jsteele22/telescopes/src/media/incoming/PXL_20240909_195538547.jpg

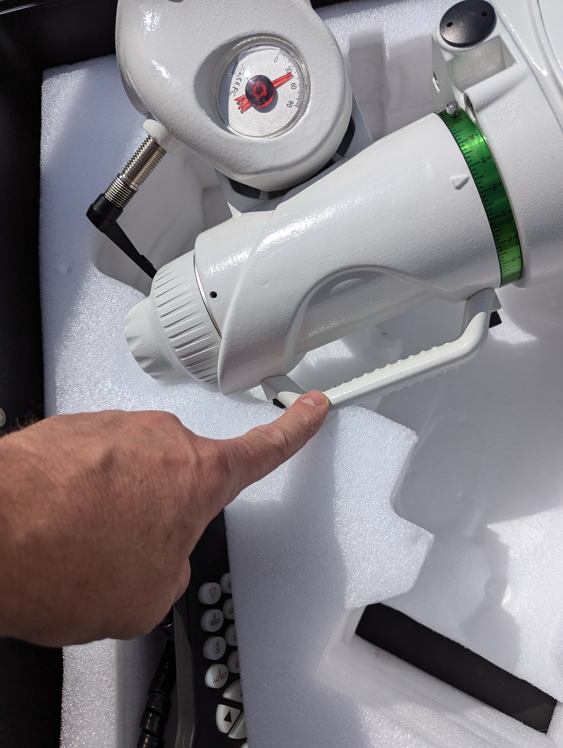
src/media/incoming/PXL_20240909_195538547.jpg
