jsteele22/telescopes/src/media/incoming/PXL_20240909_195637339.jpg

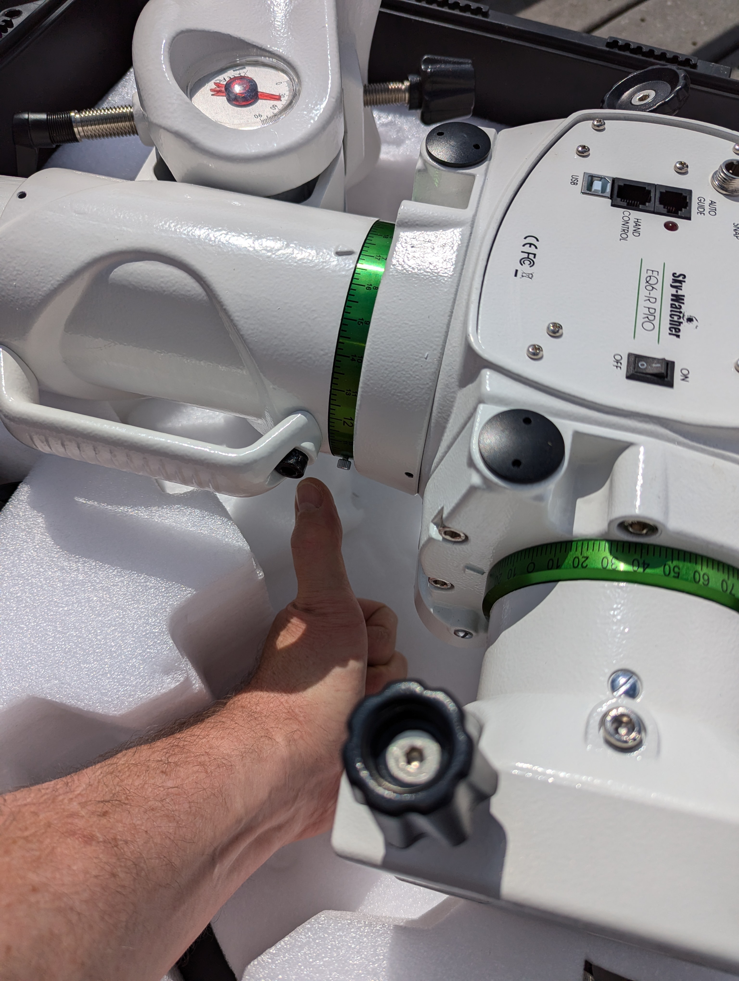
src/media/incoming/PXL_20240909_195637339.jpg
