jsteele22/telescopes/src/media/incoming/PXL_20240909_200801944.jpg

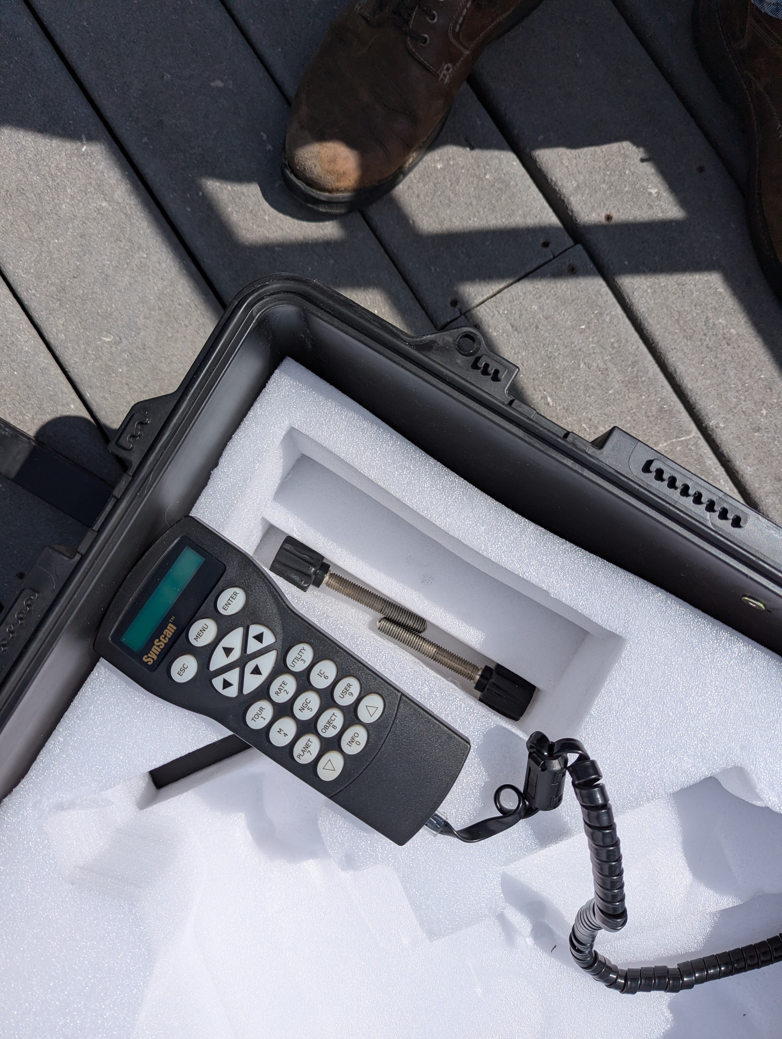
src/media/incoming/PXL_20240909_200801944.jpg
