jsteele22/telescopes/src/media/incoming/PXL_20240909_200844961.jpg

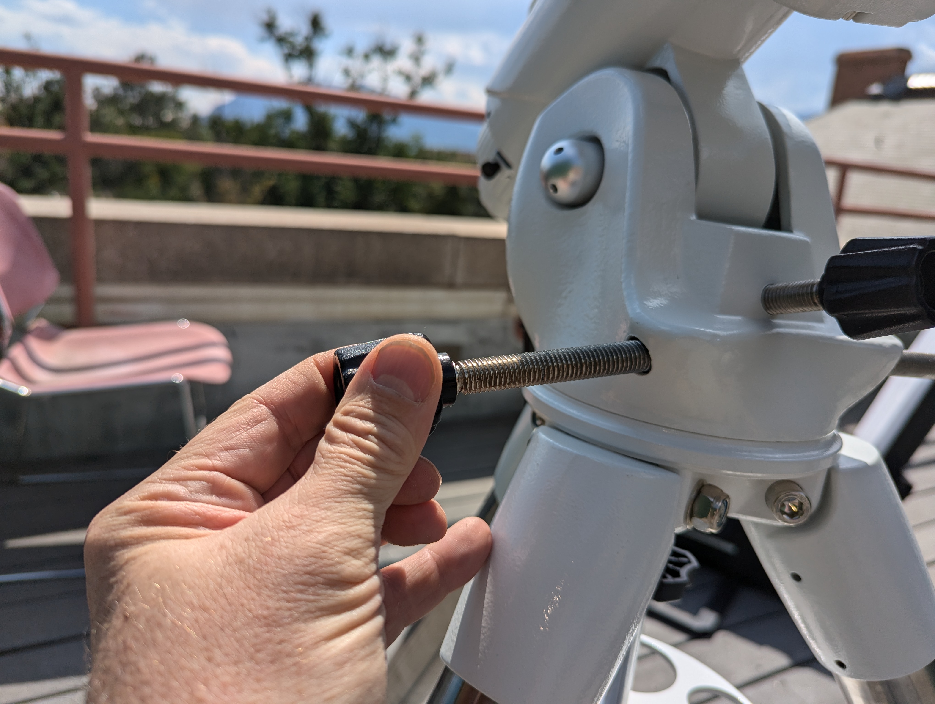
src/media/incoming/PXL_20240909_200844961.jpg
