jsteele22/telescopes/src/media/incoming/PXL_20240909_201119024.PANO.jpg

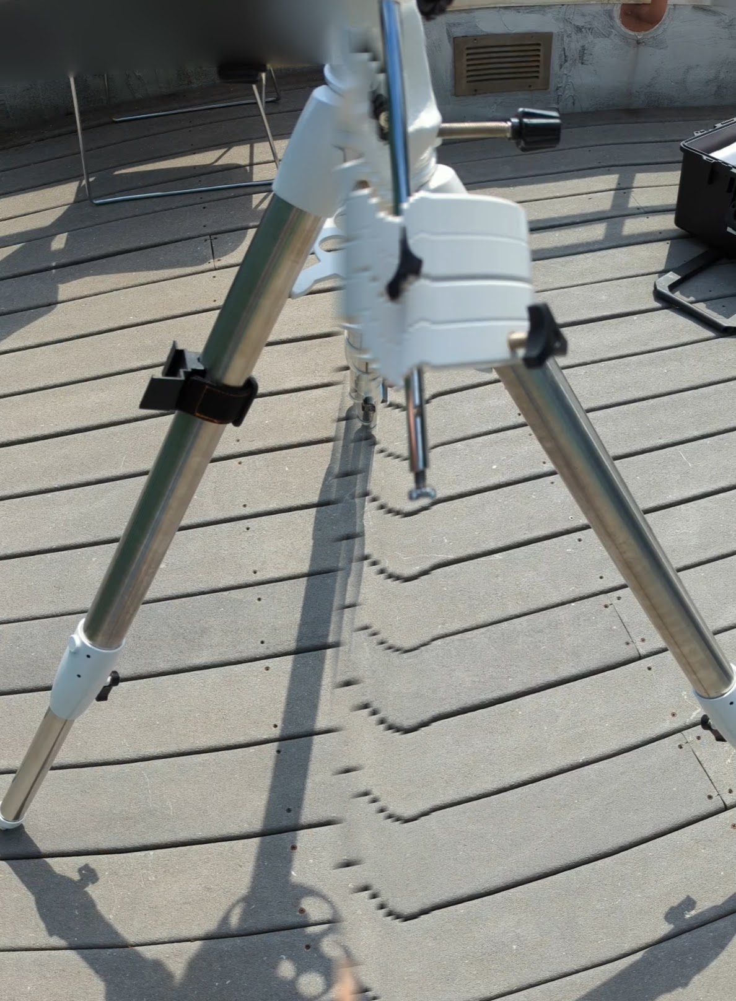
src/media/incoming/PXL_20240909_201119024.PANO.jpg
