jsteele22/telescopes/src/media/incoming/PXL_20240909_201218590.jpg

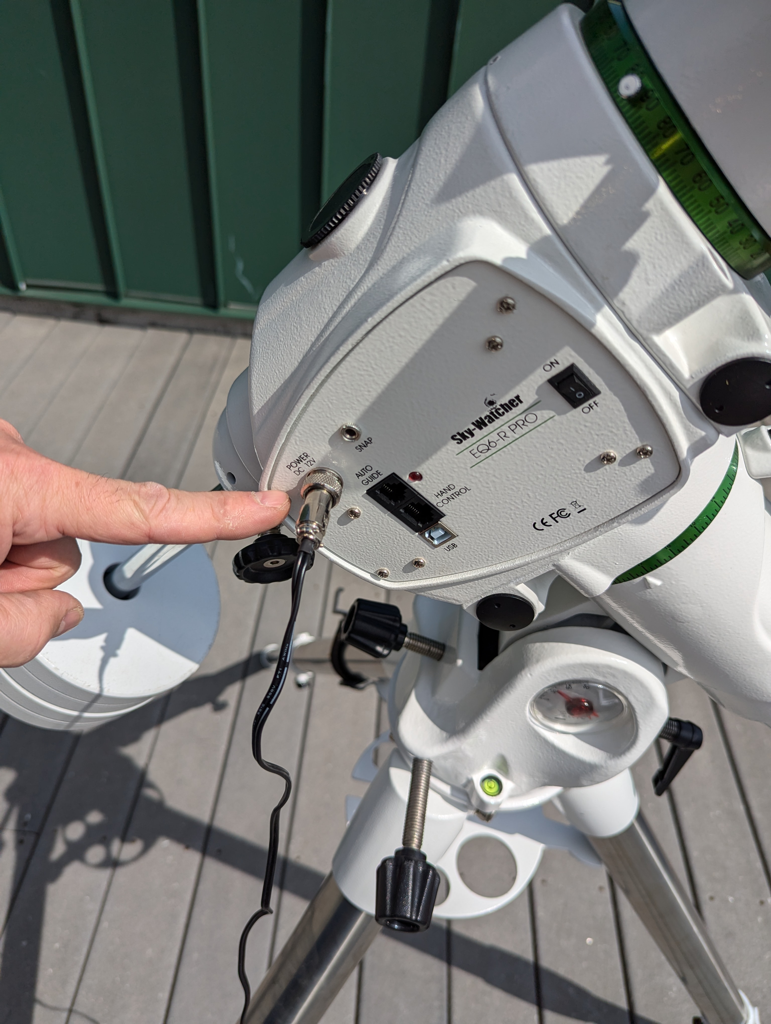
src/media/incoming/PXL_20240909_201218590.jpg
