jsteele22/telescopes/src/media/incoming/PXL_20240910_205359571.jpg

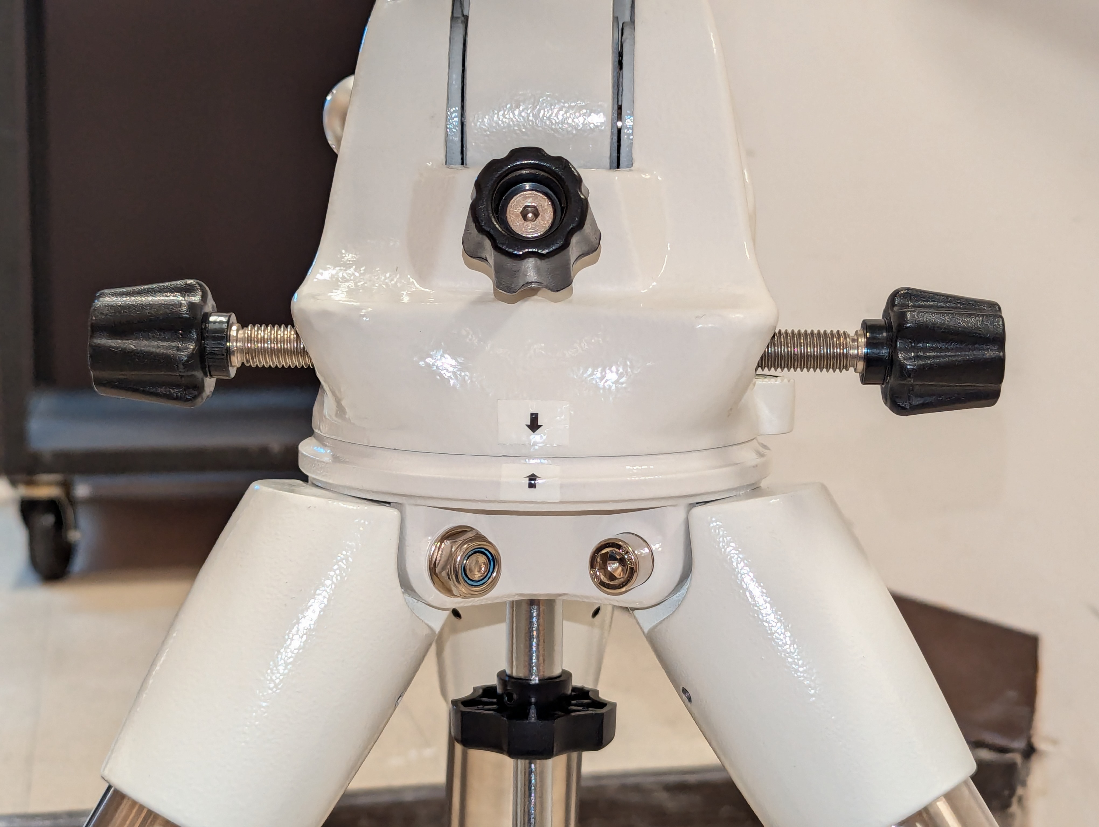
src/media/incoming/PXL_20240910_205359571.jpg
