jsteele22/telescopes/src/media/incoming/PXL_20240910_215625529.jpg

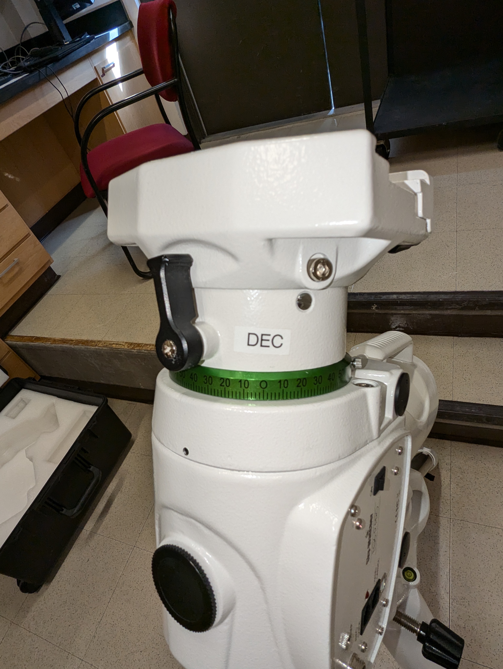
src/media/incoming/PXL_20240910_215625529.jpg
