jsteele22/telescopes/src/media/incoming/PXL_20240910_215647571.jpg

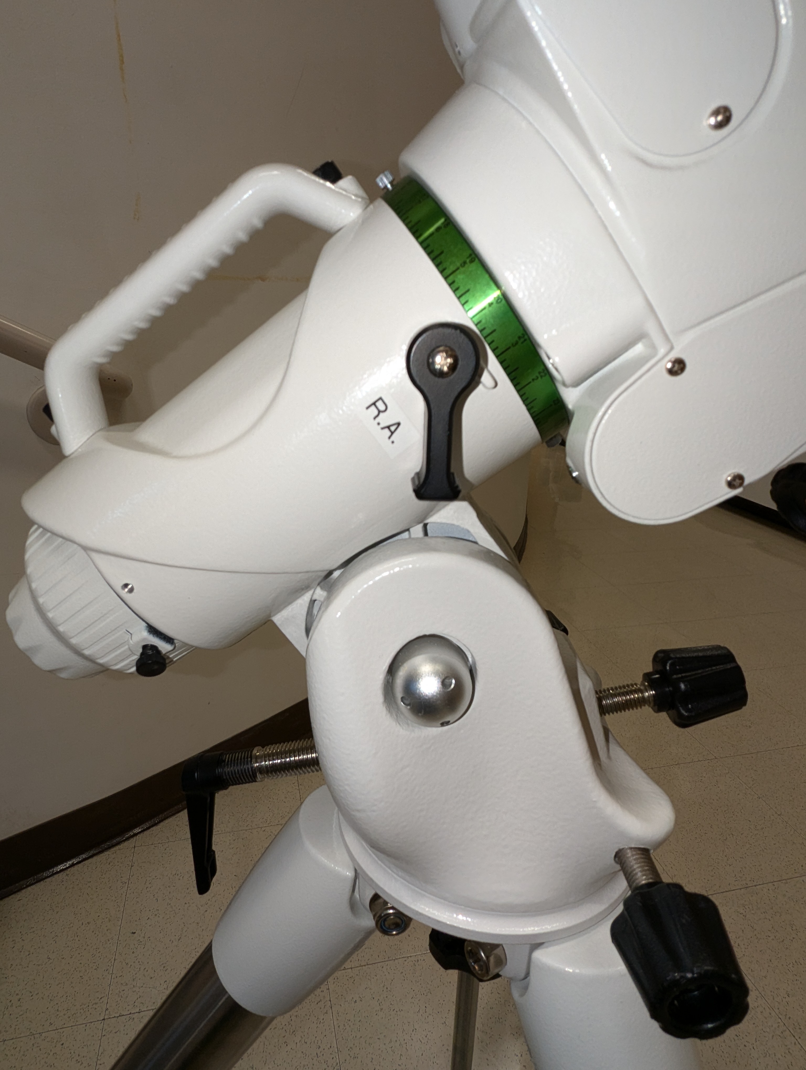
src/media/incoming/PXL_20240910_215647571.jpg
