jsteele22/telescopes/src/media/incoming/PXL_20240910_215757097.jpg

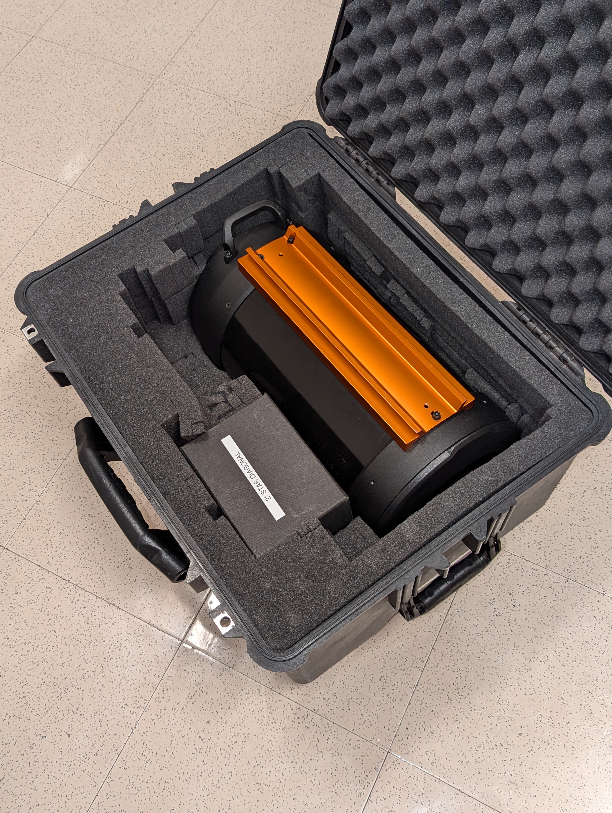
src/media/incoming/PXL_20240910_215757097.jpg
