jsteele22/telescopes/src/media/incoming/PXL_20240910_220001010.jpg

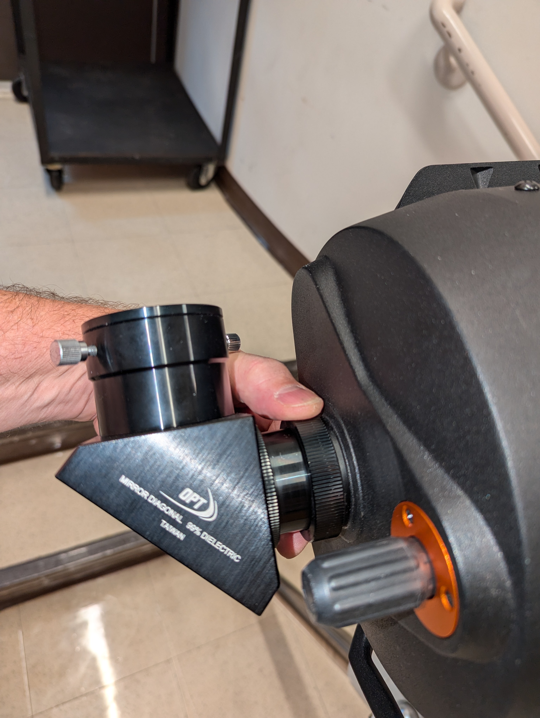
src/media/incoming/PXL_20240910_220001010.jpg
