jsteele22/telescopes/src/media/incoming/PXL_20240910_220033113.jpg

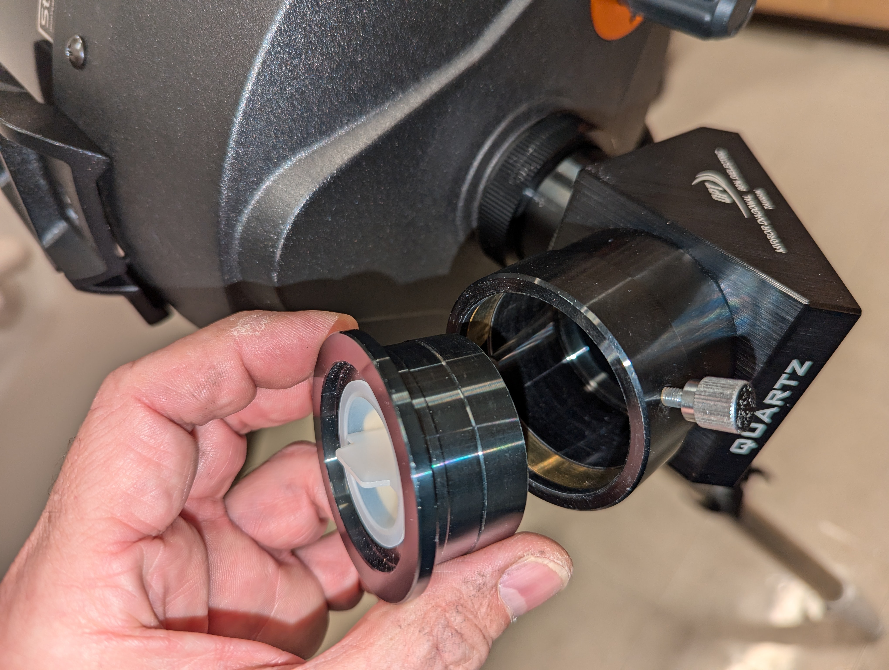
src/media/incoming/PXL_20240910_220033113.jpg
