jsteele22/telescopes/src/media/incoming/PXL_20240910_220900610.jpg

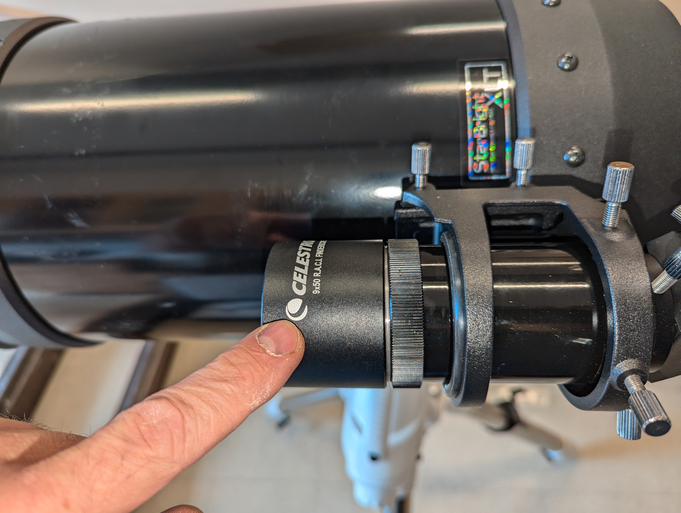
src/media/incoming/PXL_20240910_220900610.jpg
