jsteele22/telescopes/src/media/incoming/PXL_20240910_220907315.jpg

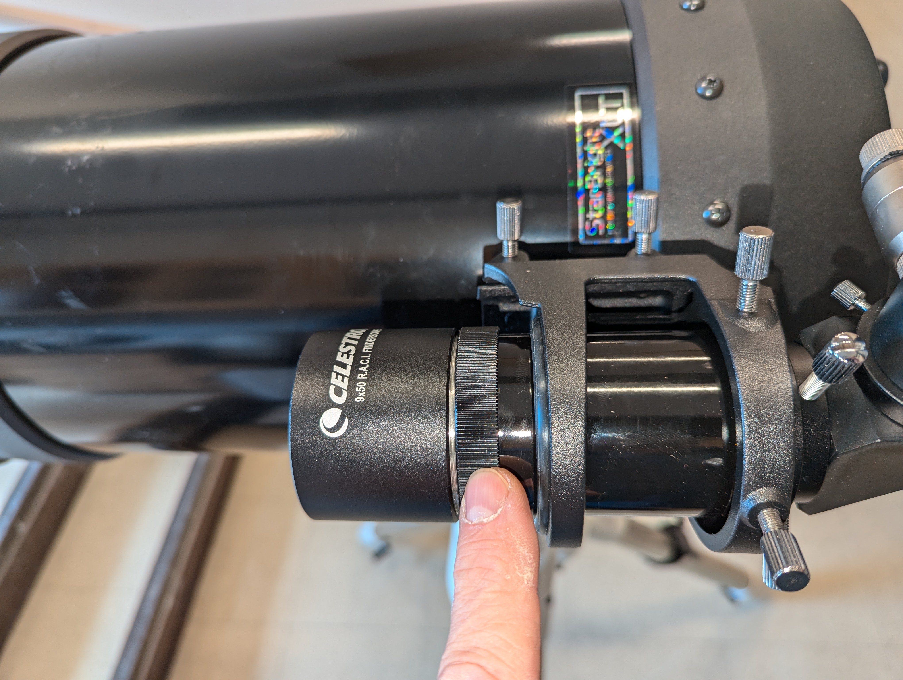
src/media/incoming/PXL_20240910_220907315.jpg
