jsteele22/telescopes/src/media/incoming/PXL_20240910_220939257.jpg

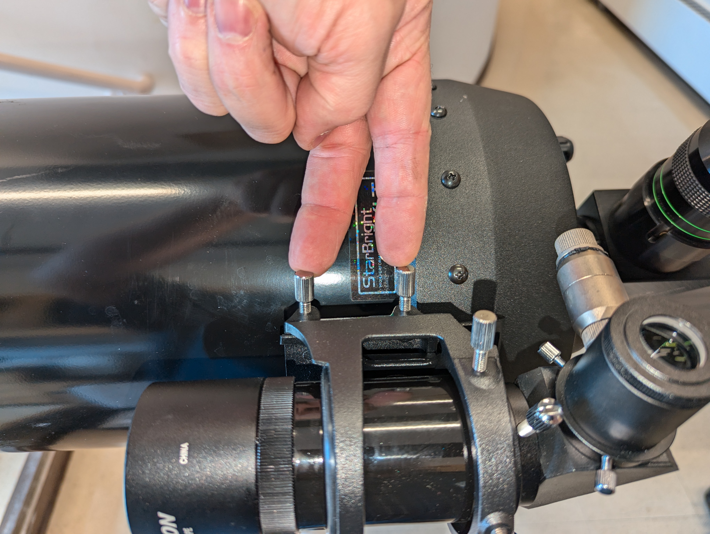
src/media/incoming/PXL_20240910_220939257.jpg
