jsteele22/telescopes/src/media/incoming/PXL_20240910_221006159.jpg

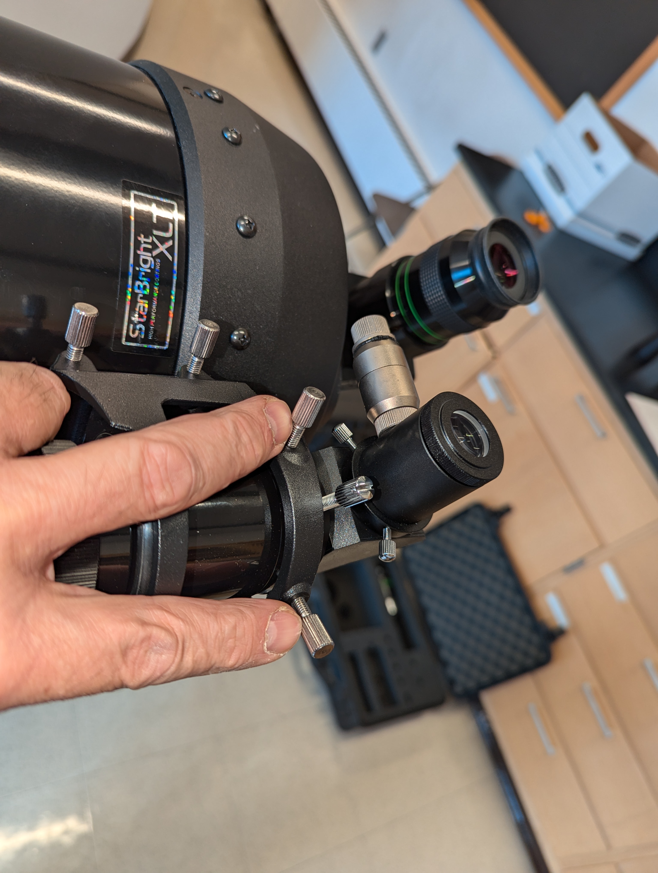
src/media/incoming/PXL_20240910_221006159.jpg
