jsteele22/telescopes/src/media/incoming/PXL_20240910_221018687.jpg

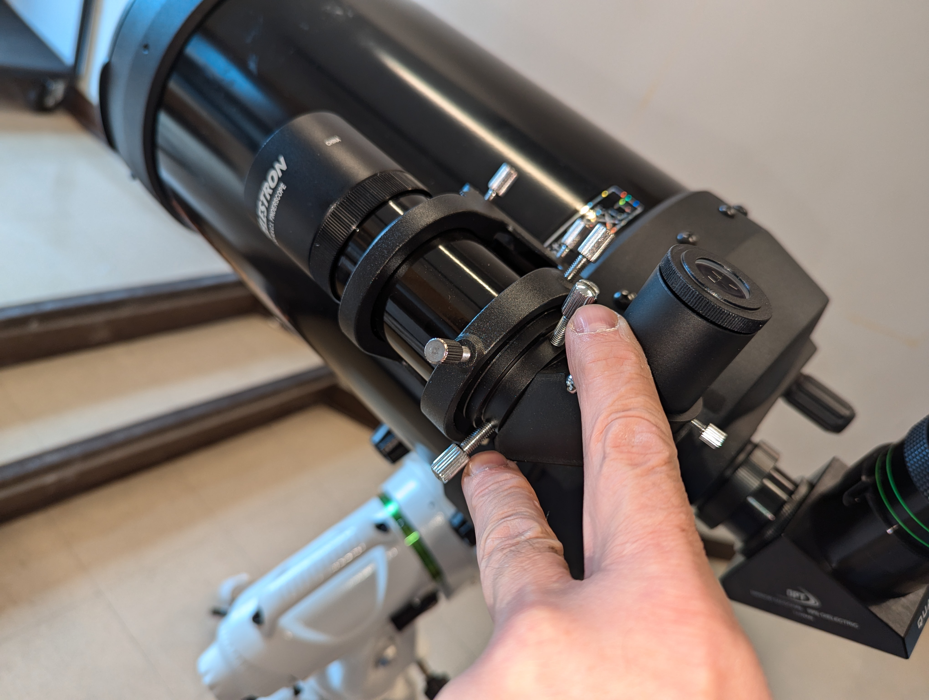
src/media/incoming/PXL_20240910_221018687.jpg
