jsteele22/telescopes/src/media/incoming/PXL_20240910_221028572.jpg

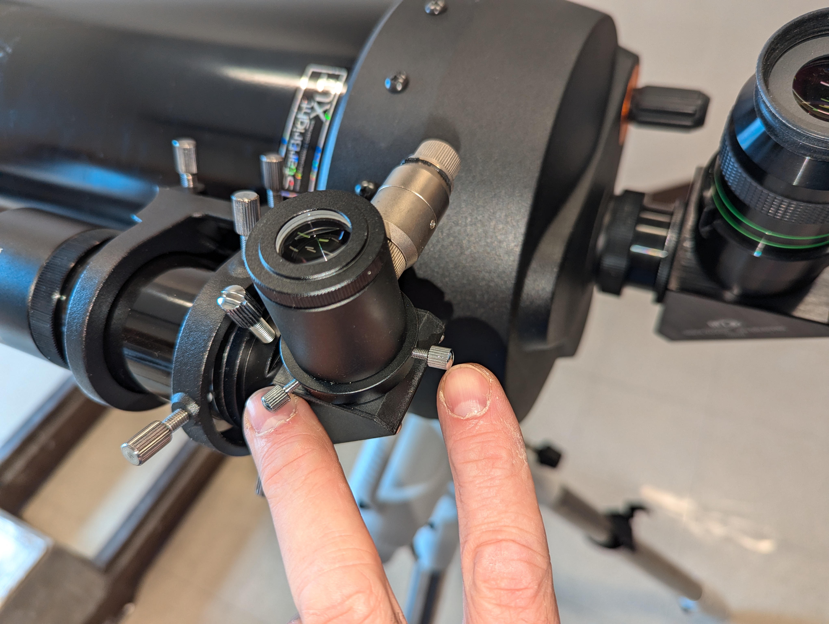
src/media/incoming/PXL_20240910_221028572.jpg
