jsteele22/telescopes/src/media/incoming/PXL_20240910_221039068.jpg

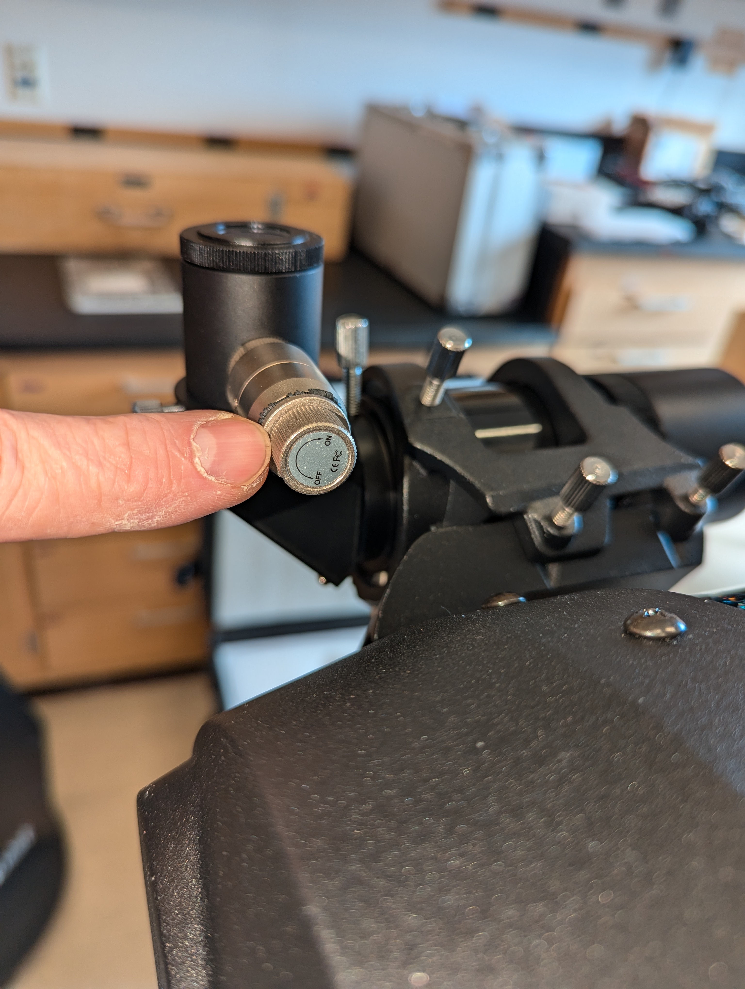
src/media/incoming/PXL_20240910_221039068.jpg
