jsteele22/telescopes/src/media/pub/eq6_DEC_clutch.jpg

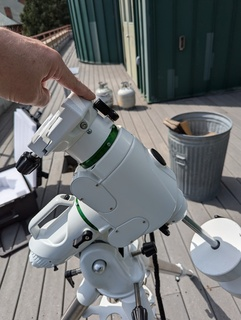
src/media/pub/eq6_DEC_clutch.jpg
