jsteele22/telescopes/src/media/raw/eq6_alignment_bolts.jpg

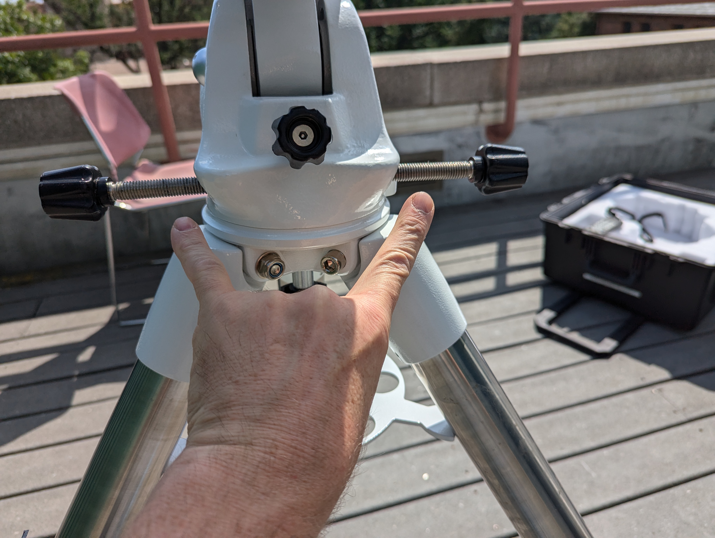
src/media/raw/eq6_alignment_bolts.jpg
