jsteele22/telescopes/src/media/raw/eq6_alignment_hole.jpg

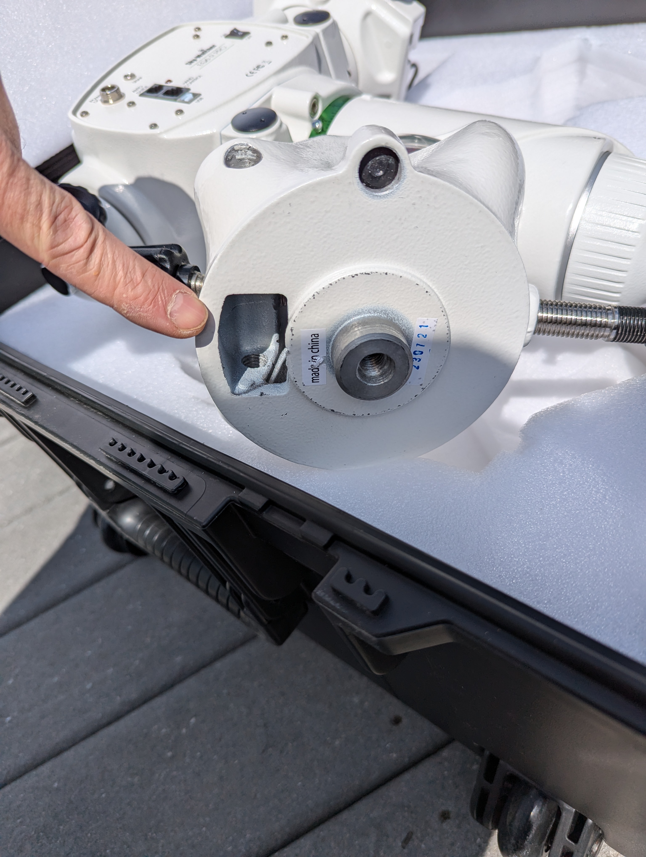
src/media/raw/eq6_alignment_hole.jpg
