jsteele22/telescopes/src/media/raw/eq6_cables.jpg

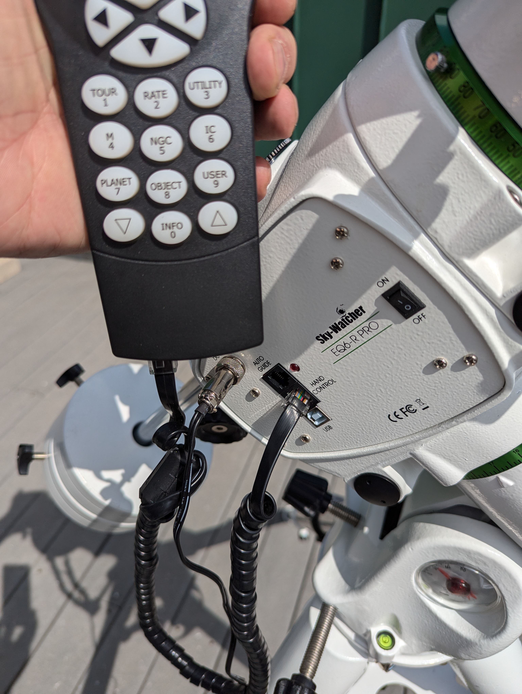
src/media/raw/eq6_cables.jpg
