jsteele22/telescopes/src/media/raw/eq6_OTA_prep.jpg

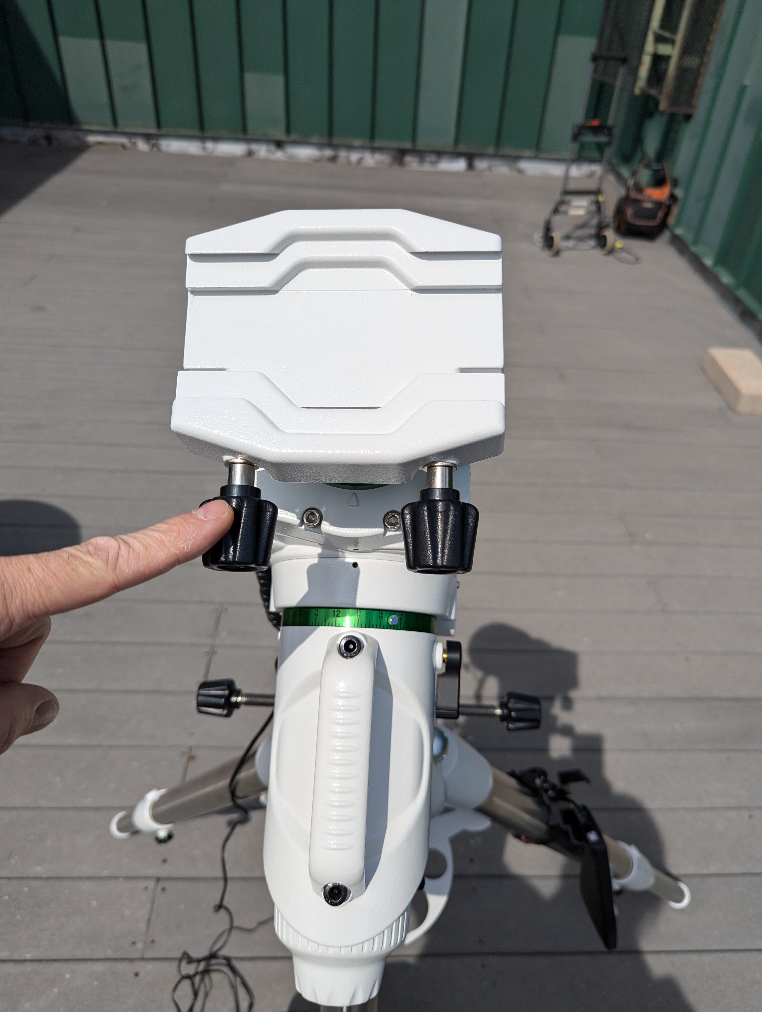
src/media/raw/eq6_OTA_prep.jpg
