jsteele22/telescopes/src/media/raw/eq6_pelican.jpg

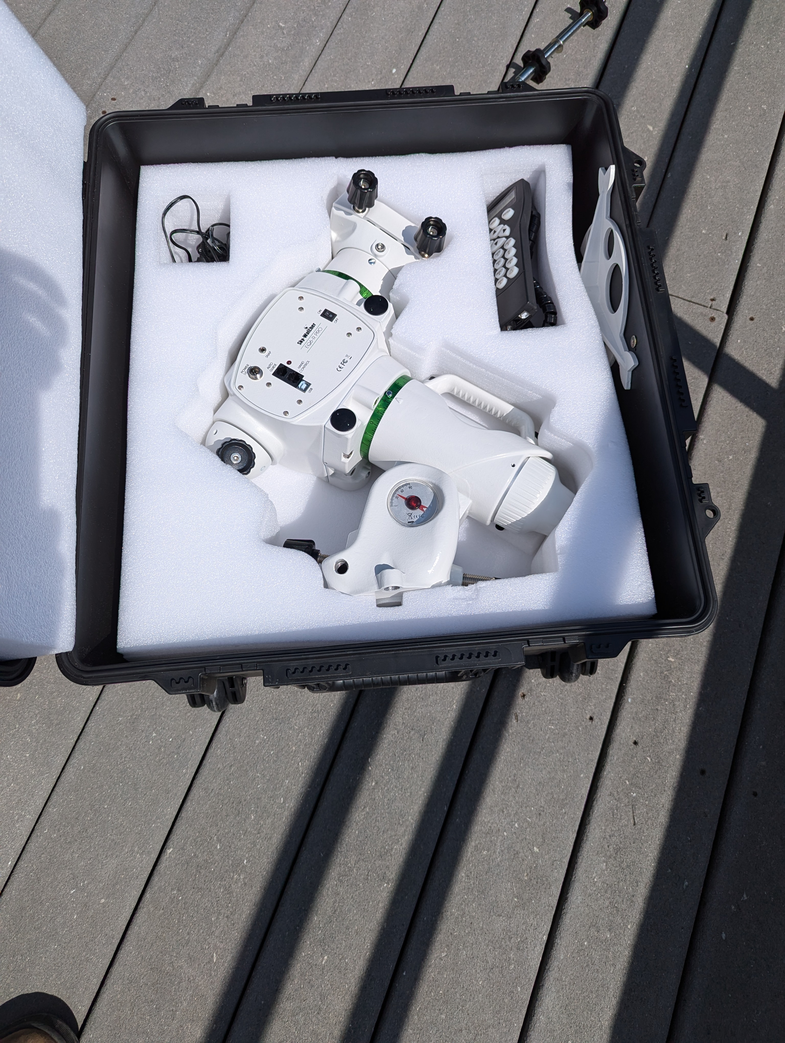
src/media/raw/eq6_pelican.jpg
