jsteele22/telescopes/src/media/raw/eq6_RA_clutch.jpg

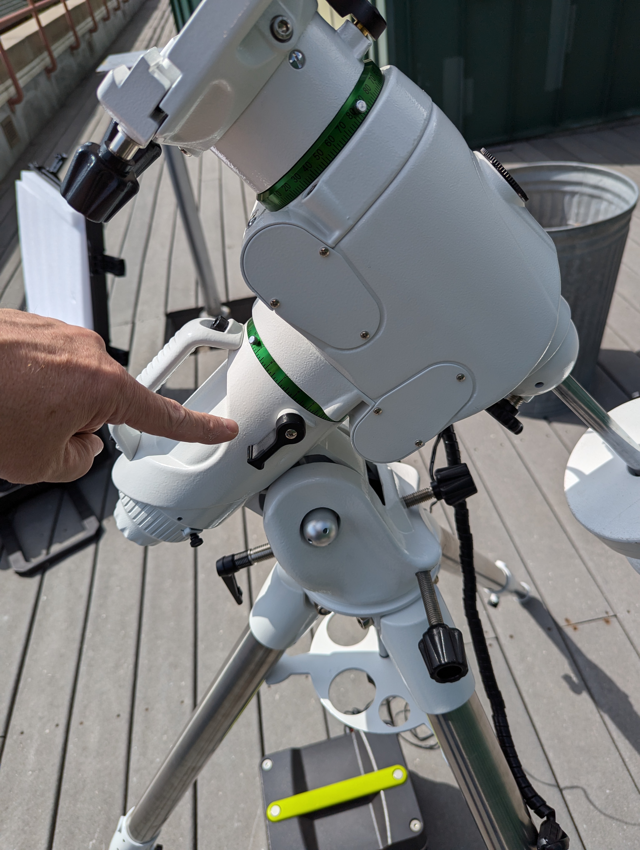
src/media/raw/eq6_RA_clutch.jpg
