jsteele22/telescopes/src/media/raw/eq6_toesaver.jpg

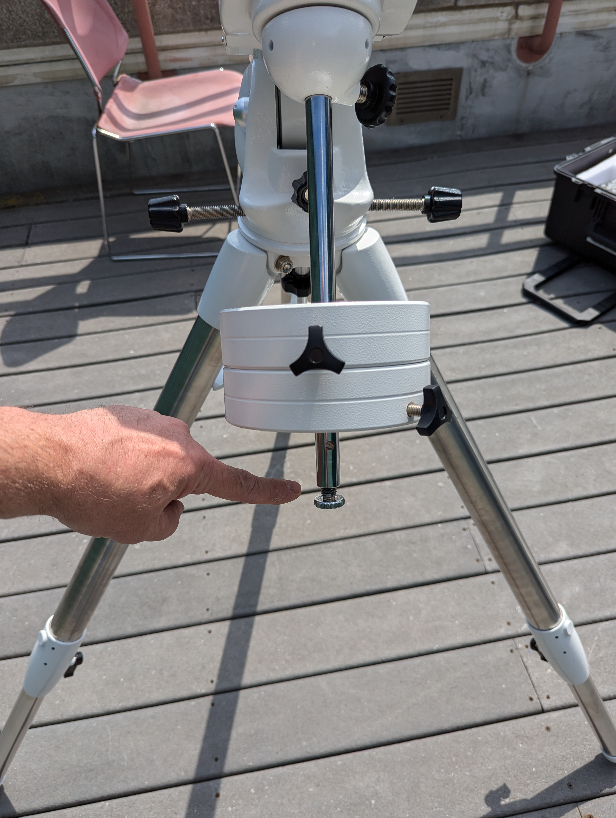
src/media/raw/eq6_toesaver.jpg
