jsteele22/telescopes/src/media/raw/eq6_tripod_top.jpg

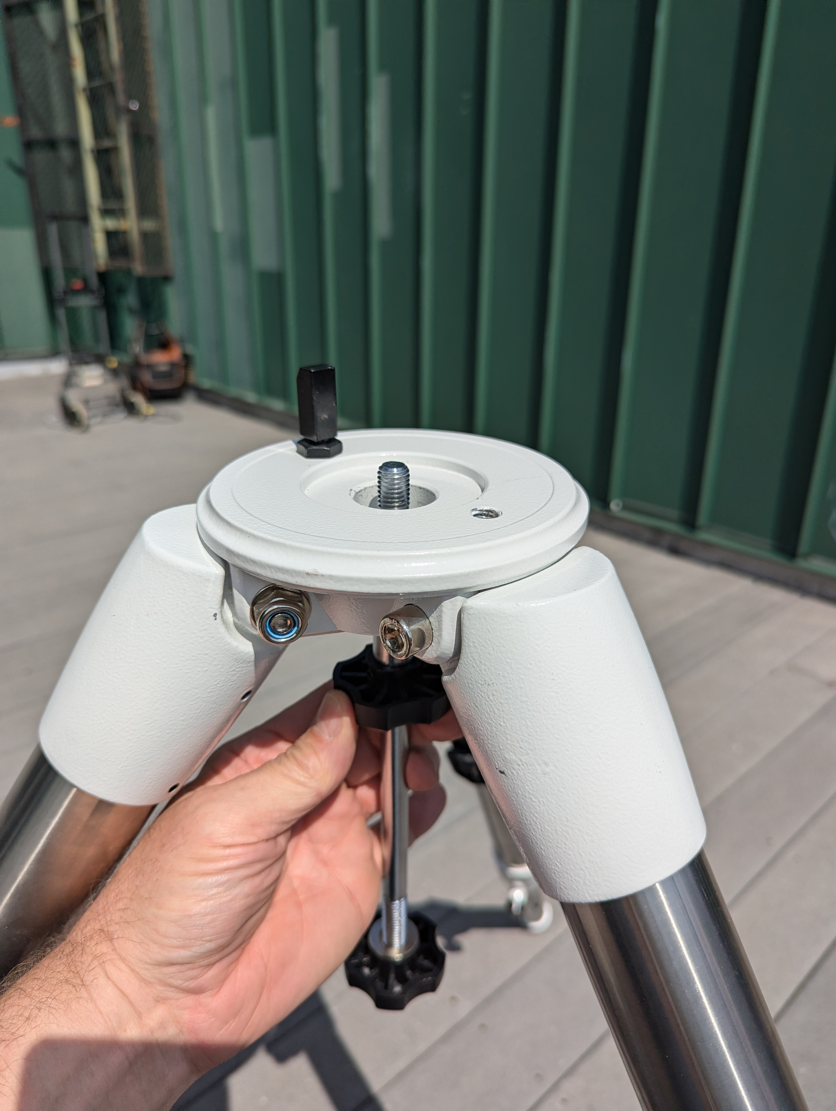
src/media/raw/eq6_tripod_top.jpg
