jsteele22/telescopes/src/media/raw/eq6_weightbar.jpg

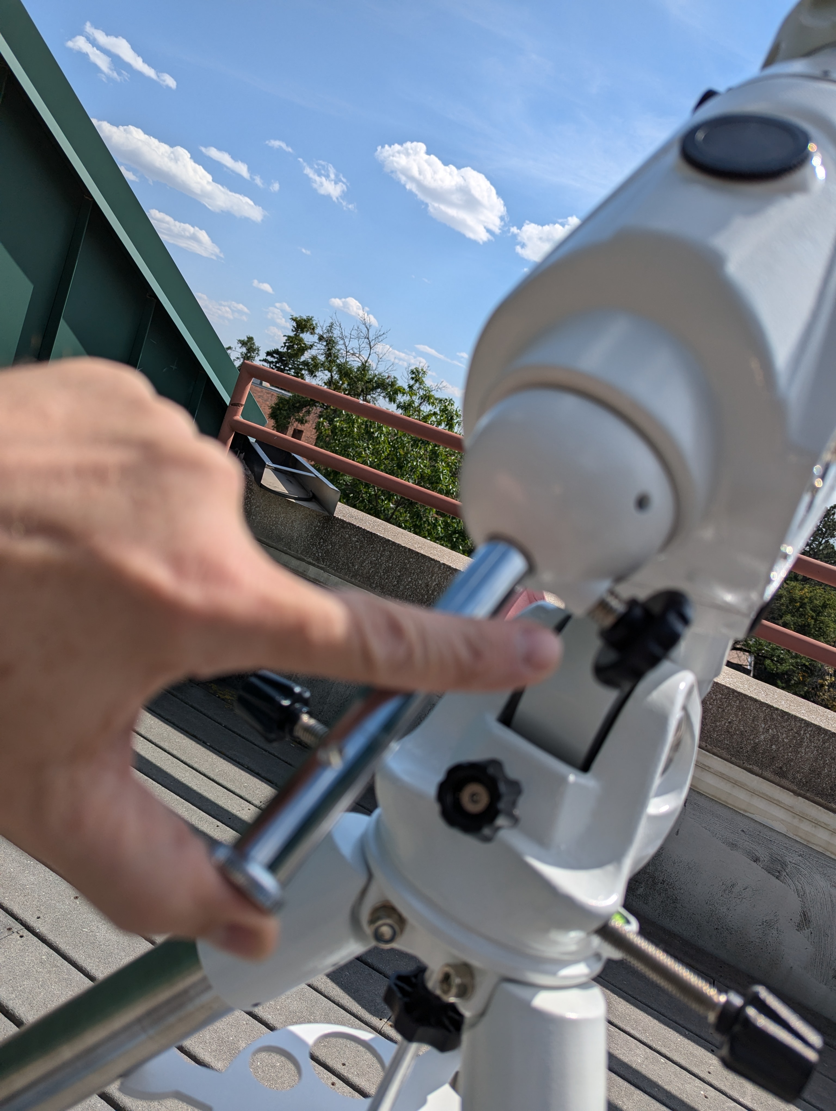
src/media/raw/eq6_weightbar.jpg
