jsteele22/telescopes/src/media/raw/lunt_ota_mark.jpg

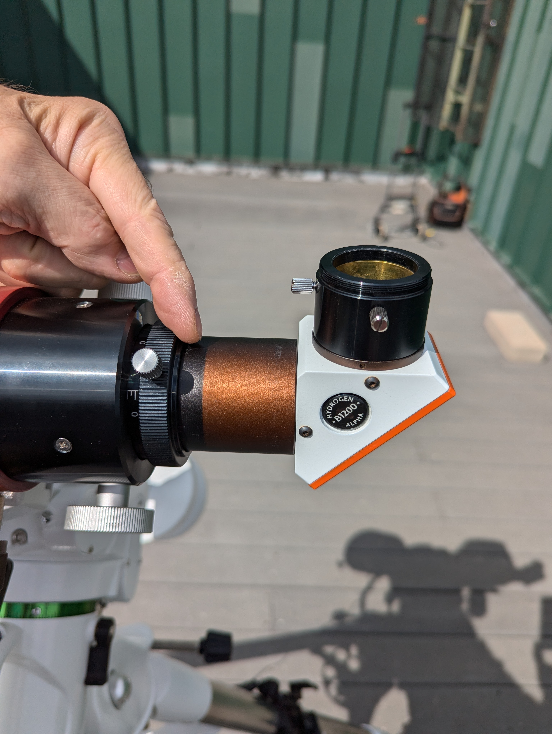
src/media/raw/lunt_ota_mark.jpg
