jsteele22/telescopes/src/media/raw/lunt_ota_screws.jpg

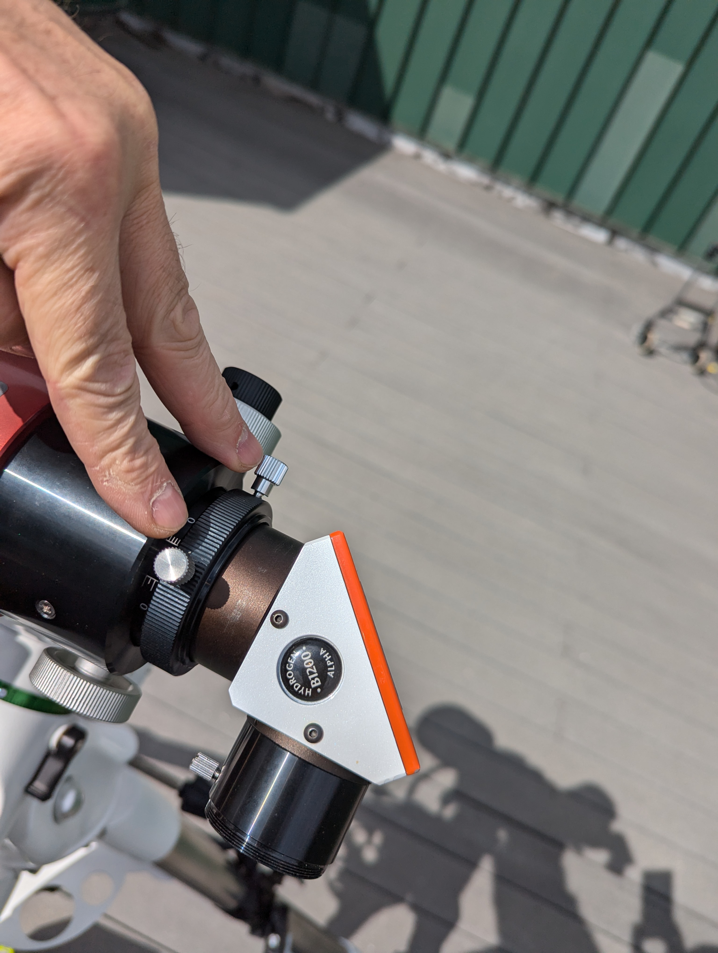
src/media/raw/lunt_ota_screws.jpg
